saewave/RemoteSwitch/Switch-4Ch-CC1101-F030F4/Src/CC1101.c

#include "CC1101.h"
#include "F030f4_Peripheral.h"
#include "rf_cmd.h"
#include <string.h>

uint8_t Transceiver_Data[64];
uint8_t Transceiver_HUB_ADDR[Transceiver_ADDR_LENGTH] = {0xAB, 0xCD};
uint8_t Transceiver_RX_ADDR[Transceiver_ADDR_LENGTH]  = {0xF0, 0xCF};

void Transceiver_Reset(void) {
    CSN_LOW();
    Delay_us(5);
    CSN_HIGH();
    Delay_us(40);
    Transceiver_WriteStrobe(0x30);
    Delay_us(2);
}

void Transceiver_SetSyncWord(uint8_t Word0, uint8_t Word1) {
    dxprintf("SetSyncWord: %2x %2x\n", Word0, Word1);
    Transceiver_WriteReg(CCxxx0_SYNC0, Word0); //CCxxx0_SYNC0
    Transceiver_WriteReg(CCxxx0_SYNC1, Word1); //CCxxx0_SYNC1
}

void Transceiver_TxMode(void) {
    Transceiver_WriteStrobe(CCxxx0_STX);
    Delay_us(10);
    Transceiver_WriteStrobe(CCxxx0_SNOP);
    Delay_us(10);
    Transceiver_WriteStrobe(CCxxx0_SNOP);
}

void Transceiver_RxMode(void) {
    Transceiver_SetSyncWord(Transceiver_RX_ADDR[0], Transceiver_RX_ADDR[1]);
    Transceiver_WriteStrobe(CCxxx0_SIDLE);
    Transceiver_WriteStrobe(CCxxx0_SFRX);
    Transceiver_WriteStrobe(CCxxx0_SRX);
    dxprintf("RxMode\n");
}

void Transceiver_SPWDMode(void) {
    Transceiver_SetSyncWord(Transceiver_RX_ADDR[0], Transceiver_RX_ADDR[1]);
    Transceiver_WriteStrobe(CCxxx0_SIDLE);
    Transceiver_WriteStrobe(CCxxx0_SPWD);
    CSN_HIGH();
    dxprintf("SPWDMode\n");
}

void Transceiver_Configure(void)
{
    uint8_t PATable[8] = {0xC0, 0xC0, 0xC0, 0xC0, 0xC0, 0xC0, 0xC0, 0xC0};
    Transceiver_WriteReg(CCxxx0_IOCFG0,0x06); //IOCFG0 - GDO0 Output Pin Configuration
    Transceiver_WriteReg(CCxxx0_FIFOTHR,0x47); //FIFOTHR - RX FIFO and TX FIFO Thresholds
    Transceiver_WriteReg(CCxxx0_PKTLEN,0x3E); //PKTLEN - Packet Length
    Transceiver_WriteReg(CCxxx0_PKTCTRL1, 0x08 + (Transceiver_ADD_RSSI_LQI ? 0x04 : 0)); //PKTCTRL1 - Packet Automation Control
    Transceiver_WriteReg(CCxxx0_PKTCTRL0,0x05); //PKTCTRL0 - Packet Automation Control
    Transceiver_WriteReg(CCxxx0_ADDR,0x23); //ADDR - Device Address
    Transceiver_WriteReg(CCxxx0_CHANNR,0x01); //CHANNR - Channel Number
    Transceiver_WriteReg(CCxxx0_FSCTRL1,0x06); //FSCTRL1 - Frequency Synthesizer Control
    Transceiver_WriteReg(CCxxx0_FREQ2,0x10); //FREQ2 - Frequency Control Word, High Byte
    Transceiver_WriteReg(CCxxx0_FREQ1,0xA7); //FREQ1 - Frequency Control Word, Middle Byte
    Transceiver_WriteReg(CCxxx0_FREQ0,0x62); //FREQ0 - Frequency Control Word, Low Byte
    Transceiver_WriteReg(CCxxx0_MDMCFG4,0xF6); //MDMCFG4 - Modem Configuration
    Transceiver_WriteReg(CCxxx0_MDMCFG3,0x43); //MDMCFG3 - Modem Configuration
    Transceiver_WriteReg(CCxxx0_MDMCFG2,0x43); //MDMCFG2 - Modem Configuration
    Transceiver_WriteReg(CCxxx0_DEVIATN,0x15); //DEVIATN - Modem Deviation Setting
    Transceiver_WriteReg(CCxxx0_MCSM0,0x18); //MCSM0 - Main Radio Control State Machine Configuration
    Transceiver_WriteReg(CCxxx0_MCSM1,0x0F); //MCSM1 - Main Radio Control State Machine Configuration
    Transceiver_WriteReg(CCxxx0_FOCCFG,0x16); //FOCCFG - Frequency Offset Compensation Configuration
    Transceiver_WriteReg(CCxxx0_WORCTRL,0xFB); //WORCTRL - Wake On Radio Control
    Transceiver_WriteReg(CCxxx0_FSCAL3,0xE9); //FSCAL3 - Frequency Synthesizer Calibration
    Transceiver_WriteReg(CCxxx0_FSCAL2,0x2A); //FSCAL2 - Frequency Synthesizer Calibration
    Transceiver_WriteReg(CCxxx0_FSCAL1,0x00); //FSCAL1 - Frequency Synthesizer Calibration
    Transceiver_WriteReg(CCxxx0_FSCAL0,0x1F); //FSCAL0 - Frequency Synthesizer Calibration
    Transceiver_WriteReg(CCxxx0_TEST2,0x81); //TEST2 - Various Test Settings
    Transceiver_WriteReg(CCxxx0_TEST1,0x35); //TEST1 - Various Test Settings
    Transceiver_WriteReg(CCxxx0_TEST0,0x09); //TEST0 - Various Test Settings
    Transceiver_WriteBurstReg(CCxxx0_PATABLE, PATable, 8);
}

void Transceiver_WriteReg(uint8_t Reg, uint8_t Value) {
    Delay_us(2);
    CSN_LOW();
    while((Transceiver_MISO_PORT->IDR & Transceiver_MISO_PIN) == Transceiver_MISO_PIN) {__NOP();};
    SPI_SendData(&Reg, 1);
    SPI_SendData(&Value, 1);
    CSN_HIGH();
}

uint8_t Transceiver_WriteStrobe(uint8_t Strobe) {
    uint8_t Res = 0;
    Delay_us(2);
    CSN_LOW();
    while((Transceiver_MISO_PORT->IDR & Transceiver_MISO_PIN) == Transceiver_MISO_PIN) {__NOP();};
//    SPI_SendData(&Strobe, 1);
    SPI_ReadData(&Res, 1, Strobe);
    while((Transceiver_MISO_PORT->IDR & Transceiver_MISO_PIN) == Transceiver_MISO_PIN) {__NOP();};
    CSN_HIGH();
    return Res;
}

void Transceiver_WriteBurstReg(uint8_t Address, uint8_t *Buf, uint8_t Length) {
    Address |= WRITE_BURST;
    Delay_us(2);
    CSN_LOW();
    while((Transceiver_MISO_PORT->IDR & Transceiver_MISO_PIN) == Transceiver_MISO_PIN) {__NOP();};
    SPI_SendData(&Address, 1);
    SPI_SendData(Buf, Length);
    CSN_HIGH();
}

uint8_t Transceiver_ReadConfigReg(uint8_t Reg) {
    uint8_t Value = 0x00;
    Reg |= READ_SINGLE;
    Delay_us(2);
    CSN_LOW();
    while((Transceiver_MISO_PORT->IDR & Transceiver_MISO_PIN) == Transceiver_MISO_PIN) {__NOP();};
    SPI_SendData(&Reg, 1);
    SPI_ReadData(&Value, 1, 0x00);
    CSN_HIGH();
    return Value;
}

uint8_t Transceiver_ReadStatusReg(uint8_t Reg) {
    uint8_t _Reg = (Reg | READ_BURST), Value = 0x00;
    Delay_us(2);
    CSN_LOW();
    while((Transceiver_MISO_PORT->IDR & Transceiver_MISO_PIN) == Transceiver_MISO_PIN) {__NOP();};
    SPI_SendData(&_Reg, 1);
    SPI_ReadData(&Value, 1, 0x00);
    CSN_HIGH();
    return Value;
}

uint8_t Transceiver_ReadBurstReg(uint8_t Reg,  uint8_t *Buff, uint8_t Length) {
    uint8_t Value = 0x00;
    Reg |= READ_BURST;
    Delay_us(2);
    CSN_LOW();
    while((Transceiver_MISO_PORT->IDR & Transceiver_MISO_PIN) == Transceiver_MISO_PIN) {__NOP();};
    SPI_SendData(&Reg, 1);
    SPI_ReadData(Buff, Length, 0x00);
    CSN_HIGH();
    return Value;
}

void Transceiver_TxTestData(void) {
    uint8_t Buf[] = {0x05, 0x48, 0x65, 0x6C, 0x6C, 0x6F};
    Transceiver_WriteStrobe(CCxxx0_SIDLE);
    Transceiver_WriteStrobe(CCxxx0_SFTX);
    Transceiver_WriteBurstReg(CCxxx0_TXFIFO, Buf, 6);
    Transceiver_WriteStrobe(CCxxx0_STX);
}

void Transceiver_TxData(uint8_t * Address, uint8_t * Buf, uint8_t Length) {
    uint8_t tBuf[Length + 1];
    tBuf[0] = Length;
    memcpy(&tBuf[1], Buf, Length);
    
#ifdef _DEBUG
        dxputs("DATA TO SEND: \n");
        for (uint8_t i = 0; i < Length+1; i++) {
            dxprintf("%x ", tBuf[i]);
        }
        dxputs("\n");
#endif
    Transceiver_SetSyncWord(Address[0], Address[1]);
    Transceiver_WriteStrobe(CCxxx0_SIDLE);
    Transceiver_WriteStrobe(CCxxx0_SFTX);
    Transceiver_WriteBurstReg(CCxxx0_TXFIFO, tBuf, Length + 1);
    Transceiver_WriteStrobe(CCxxx0_STX);
}

void Transceiver_HandleStatus(void) {
    dxputs("-------------------\n");
    SPI_FlushRxFifo();
    uint8_t Status = Transceiver_WriteStrobe(CCxxx0_SNOP | 0x80);
    dxprintf("Status: %x\n", Status);
    if (Status & FIFO_BYTES_MASK) {
        uint8_t Length = Transceiver_ReadStatusReg(CCxxx0_RXFIFO);
        dxprintf("Length: %d\n", Length);
//        Length = Length == 0 ? 10 : Length;
        if (Length & BYTES_IN_RXFIFO) {
            Transceiver_ReadBurstReg(CCxxx0_RXFIFO, Transceiver_Data, Length + (Transceiver_ADD_RSSI_LQI ? 2 : 0));
#ifdef _DEBUG
            dxputs("DATA: \n");
            for (uint8_t i = 0; i < Length; i++) {
                dxprintf("%x ", Transceiver_Data[i]);
            }
            dxputs("\n");
#endif
#if Transceiver_ADD_RSSI_LQI == 1
            uint8_t rssi, lqi; 
            unsigned char crssi;
            unsigned char clqi;
            rssi = Transceiver_Data[Length + 2 - 2];
            lqi = Transceiver_Data[Length + 2 - 1];
            if (rssi >= 128) {
                crssi = 255 - rssi;
                crssi /= 2;
                crssi += 74;
            } else {
                crssi = rssi/2;
                crssi += 74;
            }
            clqi = 0x3F - (lqi & 0x3F);
            dxprintf("crssi: %d, clqi: %d\n", crssi, clqi);
            UNUSED(clqi);
#endif
            ProcessData(Transceiver_Data, Length);
        }
    }

    if (((Status & CHIP_STATE_MASK) != 0x10) && ((Status & BYTES_IN_RXFIFO) == 0)) {
#if SAE_ALL_TIME_RX_MODE == 0x01
        Transceiver_RxMode();
#elif SAE_ALL_TIME_SPWD_MODE == 0x01
        Transceiver_SPWDMode();
#endif
    }
}

uint8_t *Transceiver_GetDeviceAddress(void)
{
    return Transceiver_RX_ADDR;
}

void Transceiver_SetHUBAddress(uint8_t *Address)
{
    memcpy(Transceiver_HUB_ADDR, Address, Transceiver_ADDR_LENGTH);
}

uint8_t *Transceiver_GetHUBAddress(void)
{
    return Transceiver_HUB_ADDR;
}

void Transceiver_SetDeviceAddress(uint8_t *Address, uint8_t Override)
{
    memcpy(Transceiver_RX_ADDR, Address, Transceiver_ADDR_LENGTH);
}

void Transceiver_SetDefaultDeviceAddress(void)
{
/*    memcpy(nRF24_Rx_Temp_Addr, nRF24_Rx_addr, 5);
    memcpy(Transceiver_RX_ADDR, nRF24_Rx_Default_Addr, 5);*/
}
