saewave/RemoteSwitch/Hub-F103-FreeRTOS/Inc/config.h

#ifndef __config_H
#define __config_H

#define SAE_CMD_BEGIN_CHAR1 0x41  // 'A'
#define SAE_CMD_BEGIN_CHAR2 0x54  // 'T'
#define SAE_CMD_BEGIN_CHAR3 0x2B  // '+'
#define SAE_CMD_LENGTH 100
#define SAE_CMD_QUEUE_LENGTH 10
#define SAE_OUTPUT_DATA_LENGTH 100
#define SAE_ENABLE_DEBUG

#define SAE_DEVICES_MEMORY_ADDRESS 0x0807F800
#define SAE_CPU_FREQUENCY 8000000

#endif /* __config_H */
