saewave/RemoteSwitch/Hub-F103-FreeRTOS/Inc/nRF24L01P.h

#include "stm32f10x.h"
#include <stdio.h>
#include <stdlib.h>
#include "at_processor.h"
#include "rf_processor.h"
#include "freertos.h"
#include "xdebug.h"
#include "F103RE_Peripheral.h"

#ifndef __nRF24L01_H
#define __nRF24L01_H

#ifdef __cplusplus
 extern "C" {
#endif 


#define T_CE_GPIO_Port GPIOC
#define R_CE_GPIO_Port GPIOA

#define T_CE_Pin GPIO_BSRR_BS6
#define R_CE_Pin GPIO_BSRR_BS9

#define T_CSN_GPIO_Port GPIOB
#define R_CSN_GPIO_Port GPIOA

#define T_CSN_Pin GPIO_BSRR_BS10
#define R_CSN_Pin GPIO_BSRR_BS10

#define T_IRQ_Pin EXTI_PR_PR12
#define R_IRQ_Pin EXTI_PR_PR11

#define GPIO_PIN_LOW 16
#define GPIO_PIN_HIGH 0
     
/* Select Radio Tx/Rx */

#define CHIP_Tx 0x00
#define CHIP_Rx 0x01
   
/* nRF24L0 commands */
#define nRF24_CMD_RREG             0x00  // R_REGISTER -> Read command and status registers
#define nRF24_CMD_WREG             0x20  // W_REGISTER -> Write command and status registers
#define nRF24_CMD_R_RX_PAYLOAD     0x61  // R_RX_PAYLOAD -> Read RX payload
#define nRF24_CMD_W_TX_PAYLOAD     0xA0  // W_TX_PAYLOAD -> Write TX payload
#define nRF24_CMD_FLUSH_TX         0xE1  // FLUSH_TX -> Flush TX FIFO
#define nRF24_CMD_FLUSH_RX         0xE2  // FLUSH_RX -> Flush RX FIFO
#define nRF24_CMD_REUSE_TX_PL      0xE3  // REUSE_TX_PL -> Reuse last transmitted payload
#define nRF24_CMD_R_RX_PL_WID      0x60  // Read RX payload width for the top R_RX_PAYLOAD in the RX FIFO.
#define nRF24_CMD_NOP              0xFF  // No operation (to read status register)

/* nRF24L0 registers */
#define nRF24_REG_CONFIG           0x00  // Configuration register
#define nRF24_REG_EN_AA            0x01  // Enable "Auto acknowledgment"
#define nRF24_REG_EN_RXADDR        0x02  // Enable RX addresses
#define nRF24_REG_SETUP_AW         0x03  // Setup of address widths
#define nRF24_REG_SETUP_RETR       0x04  // Setup of automatic retranslation
#define nRF24_REG_RF_CH            0x05  // RF channel
#define nRF24_REG_RF_SETUP         0x06  // RF setup register
#define nRF24_REG_STATUS           0x07  // Status register
#define nRF24_REG_OBSERVE_TX       0x08  // Transmit observe register
#define nRF24_REG_CD               0x09  // Carrier detect
#define nRF24_REG_RX_ADDR_P0       0x0A  // Receive address data pipe 0
#define nRF24_REG_RX_ADDR_P1       0x0B  // Receive address data pipe 1
#define nRF24_REG_RX_ADDR_P2       0x0C  // Receive address data pipe 2
#define nRF24_REG_RX_ADDR_P3       0x0D  // Receive address data pipe 3
#define nRF24_REG_RX_ADDR_P4       0x0E  // Receive address data pipe 4
#define nRF24_REG_RX_ADDR_P5       0x0F  // Receive address data pipe 5
#define nRF24_REG_TX_ADDR          0x10  // Transmit address
#define nRF24_REG_RX_PW_P0         0x11  // Number of bytes in RX payload id data pipe 0
#define nRF24_REG_RX_PW_P1         0x12  // Number of bytes in RX payload id data pipe 1
#define nRF24_REG_RX_PW_P2         0x13  // Number of bytes in RX payload id data pipe 2
#define nRF24_REG_RX_PW_P3         0x14  // Number of bytes in RX payload id data pipe 3
#define nRF24_REG_RX_PW_P4         0x15  // Number of bytes in RX payload id data pipe 4
#define nRF24_REG_RX_PW_P5         0x16  // Number of bytes in RX payload id data pipe 5
#define nRF24_REG_FIFO_STATUS      0x17  // FIFO status register
#define nRF24_REG_DYNPD            0x1C  // Enable dynamic payload length
#define nRF24_REG_FEATURE          0x1D  // Feature register

/* nRF24L0 bits */
#define nRF24_MASK_RX_DR           0x40  // Mask interrupt caused by RX_DR
#define nRF24_MASK_TX_DS           0x20  // Mask interrupt caused by TX_DS
#define nRF24_MASK_MAX_RT          0x10  // Mask interrupt caused by MAX_RT
#define nRF24_MASK_PWR_UP          0x02  // Mask PWR_UP 
#define nRF24_FIFO_RX_EMPTY        0x01  // RX FIFO empty flag
#define nRF24_FIFO_RX_FULL         0x02  // RX FIFO full flag

/* Some constants */
#define nRF24_RX_ADDR_WIDTH        5    // nRF24 RX address width
#define nRF24_TX_ADDR_WIDTH        5    // nRF24 TX address width
#define SPI_TIMEOUT                1000

/* Variables */
extern uint8_t nRF24_HUB_addr[nRF24_RX_ADDR_WIDTH];
extern uint8_t nRF24_NET_TX_START_addr[nRF24_TX_ADDR_WIDTH];
extern uint8_t nRF24_DEVICE_CFG_addr[nRF24_TX_ADDR_WIDTH];


/* Function prototypes */
//void nRF24_init();

void nRF24_Configure(void);
void nRF24_GetDeviceFullAddress(uint16_t ShortAddress, uint8_t *FullAddress);
void nRF24_RXMode(SPI_TypeDef* hspi);
void nRF24_TXMode(SPI_TypeDef* hspi);
uint8_t nRF24_TXPacket(SPI_TypeDef* hspi, uint8_t *nRF24_TX_addr, uint8_t *pBuf, uint8_t Length);
void nRF24_RXPacket(SPI_TypeDef* hspi,uint8_t* pBuf, uint8_t* Length);
void nRF24_RWReg(SPI_TypeDef* hspi, uint8_t Chip, uint8_t Reg, uint8_t Data);
uint8_t nRF24_ReadReg(SPI_TypeDef* hspi, uint8_t Chip, uint8_t Reg);
void nRF24_WriteBuf(SPI_TypeDef* hspi, uint8_t Chip, uint8_t Reg, uint8_t *Data, uint8_t size);
void nRF24_ReadBuf(SPI_TypeDef* hspi, uint8_t Chip, uint8_t Reg, uint8_t *Data, uint8_t count);
uint8_t nRF24_DataReady(SPI_TypeDef* hspi);
void nRF24_DumpRegisters(SPI_TypeDef* hspi, uint8_t Chip);
uint8_t nRF24_SendCmd(SPI_TypeDef* hspi, uint8_t Chip, uint8_t Cmd);
uint8_t nRF24_GetStatus(SPI_TypeDef* hspi, uint8_t Chip);
void nRF24_HandleStatus(SPI_TypeDef* hspi, uint8_t Chip);
void nRF24_SetCE(uint8_t Chip, uint8_t PinState);
void nRF24_SetCSN(uint8_t Chip, uint8_t PinState);

static void SPIx_Error (void);

static void SPIx_Write(uint8_t Value);
static uint32_t SPIx_Read(void);

#ifdef __cplusplus
}
#endif

#endif /* __nRF24L01_H */
