saewave/RemoteSwitch/Nucleo401RE_RTOS/Inc/config.h

#ifndef __config_H
#define __config_H

#define AS_CMD_BEGIN_CHAR1 0x41  // 'A'
#define AS_CMD_BEGIN_CHAR2 0x54  // 'T'
#define AS_CMD_BEGIN_CHAR3 0x2B  // '+'
#define AS_CMD_LENGTH 100
#define AS_CMD_END_CHAR 0x0D

#endif /* __config_H */
