saewave/RemoteSwitch/Hub-F103-USB-Stick-SI446x/Inc/F103RE_Peripheral.h

#include "stm32f10x.h"
#include "stdint.h"
#include "xdebug.h"
#include "config.h"

#define SYS_FREQUENCY 72000000UL
#define APB1CLK 72000000UL
#define APB2CLK 72000000UL
#define BAUDRATE 115200UL
#define USART_BUF_LEN 50

#define SET_BIT(REG, BIT)     ((REG) |= (BIT))
#define CLEAR_BIT(REG, BIT)   ((REG) &= ~(BIT))
#define READ_BIT(REG, BIT)    ((REG) & (BIT))
#define CLEAR_REG(REG)        ((REG) = (0x0))
#define WRITE_REG(REG, VAL)   ((REG) = (VAL))
#define READ_REG(REG)         ((REG))
#define MODIFY_REG(REG, CLEARMASK, SETMASK)  WRITE_REG((REG), (((READ_REG(REG)) & (~(CLEARMASK))) | (SETMASK)))
#define UNUSED(x) ((void)(x))
#define OUSART1 0x00
#define OUSART2 0x01

#define CSN_LOW()      GPIOC->BSRR = GPIO_BSRR_BR13
#define CSN_HIGH()     GPIOC->BSRR = GPIO_BSRR_BS13

#define Transceiver_CTS_PORT GPIOA
#define Transceiver_CTS_PIN  GPIO_IDR_IDR3

#define DWT_CYCCNT    *(volatile uint32_t *)0xE0001004
#define DWT_CONTROL   *(volatile uint32_t *)0xE0001000
#define SCB_DEMCR     *(volatile uint32_t *)0xE000EDFC
#define FLASH_FKEY1   0x45670123
#define FLASH_FKEY2   0xCDEF89AB

#define UART_DIV_SAMPLING16(_PCLK_, _BAUD_)         (((_PCLK_)*25)/(4*(_BAUD_)))
#define UART_DIVMANT_SAMPLING16(_PCLK_, _BAUD_)     (UART_DIV_SAMPLING16((_PCLK_), (_BAUD_))/100)
#define UART_DIVFRAQ_SAMPLING16(_PCLK_, _BAUD_)     (((UART_DIV_SAMPLING16((_PCLK_), (_BAUD_)) - (UART_DIVMANT_SAMPLING16((_PCLK_), (_BAUD_)) * 100)) * 16 + 50) / 100)

#define UART_BRR_SAMPLING16(_PCLK_, _BAUD_)            (((UART_DIVMANT_SAMPLING16((_PCLK_), (_BAUD_)) << 4) + \
                                                        (UART_DIVFRAQ_SAMPLING16((_PCLK_), (_BAUD_)) & 0xF0)) + \
                                                        (UART_DIVFRAQ_SAMPLING16((_PCLK_), (_BAUD_)) & 0x0F))

void RCC_Configure(void);
void CRC_Configure(void);
void DWT_Configure(void);
void System_Configure (void);
void RTC_Configure (void);
void RTC_Time_Configure(uint8_t hh, uint8_t mm, uint8_t ss);
void RTC_Alarm_Configure(uint8_t hh, uint8_t mm, uint8_t ss);
void RTC_WakeUp_Configure(uint16_t Period);
void USART_Configure(void);
void SPI_Configure (void);
void GPIO_Configure (void);
void EXTI_Configure(void);
void TIM_Configure (void);
  
void SPI_SendData(SPI_TypeDef * SPI, uint8_t *Data, uint16_t Length);
void SPI_ReadRxFifoData(SPI_TypeDef *SPI, uint8_t *Data, uint16_t Length);
void SPI_ReadData(SPI_TypeDef * SPI, uint8_t *Data, uint16_t Length, uint8_t Dummy);
void SPI_FlushRxFifo(void);

void USART_SendChar(USART_TypeDef * USART, unsigned char ch);
void USART_SendData(USART_TypeDef * USART, uint8_t *Data, uint16_t Length);
void USART_DMASendData(USART_TypeDef *USART, char *Data, uint16_t Length);
    
void FLASH_WriteData(uint32_t fAddress, uint8_t *Data, int Size,
                     uint32_t EraseAddress);
void FLASH_Erase(uint32_t EraseAddress, uint8_t Pages);

void WWDG_Configure(void);
void WWDG_Update(void);
    
void GOTO_Sleep(void);
void GOTO_Stop(void);

void uEXTI_IRQHandler(uint32_t Pin);
void uTIM_IRQHandler(TIM_TypeDef *Tim);
void uRTC_IRQHandler(uint32_t RTC_ISR);
void uUSART_IRQHandler(USART_TypeDef * USART, uint32_t SR, uint8_t * Data, uint8_t Length);
void Delay_ms(uint32_t Delay);
void Delay_us(uint32_t Delay);
